ebrahimk/AquaSense/mechanical/photos/20190828_182527.jpg

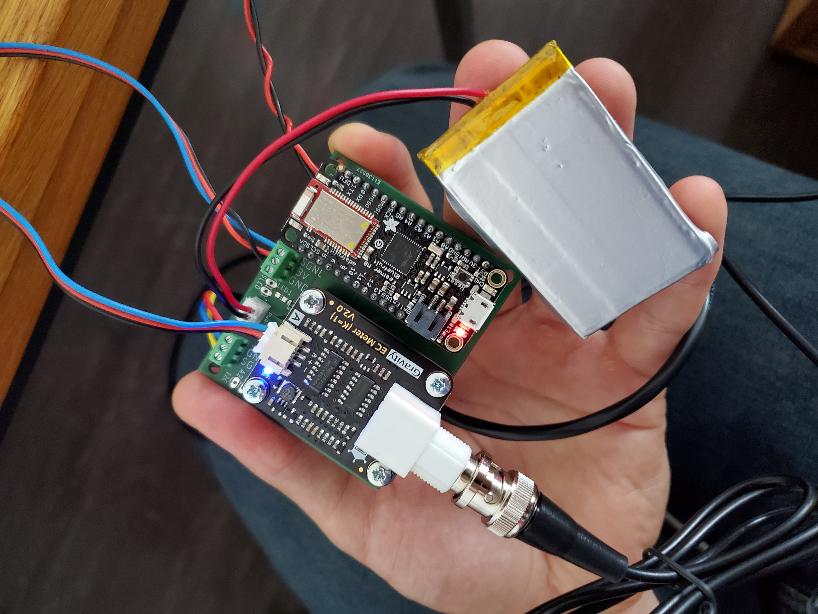
mechanical/photos/20190828_182527.jpg
