ebrahimk/AquaSense/mechanical/photos/20190830_155901.jpg

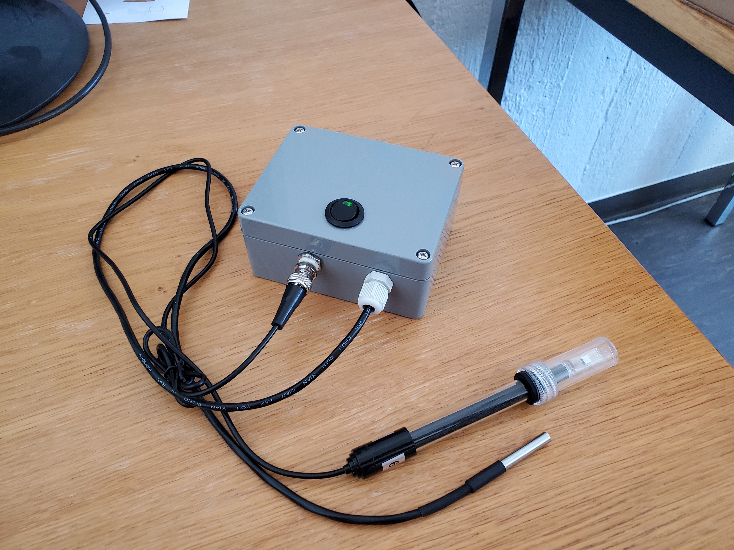
mechanical/photos/20190830_155901.jpg
